ccadic/SHARPIW0/20211212_194929.jpg

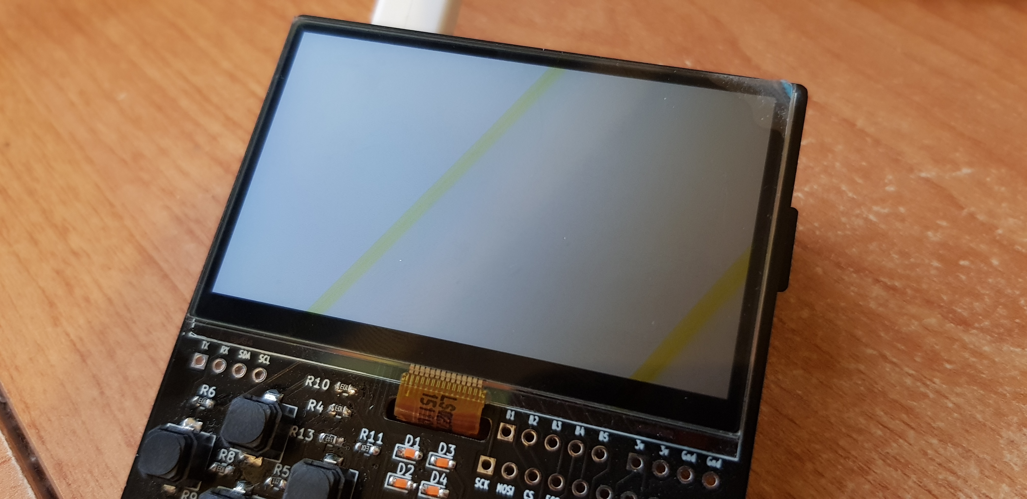
20211212_194929.jpg
