ccadic/SHARPIW0/20211215_131525.jpg

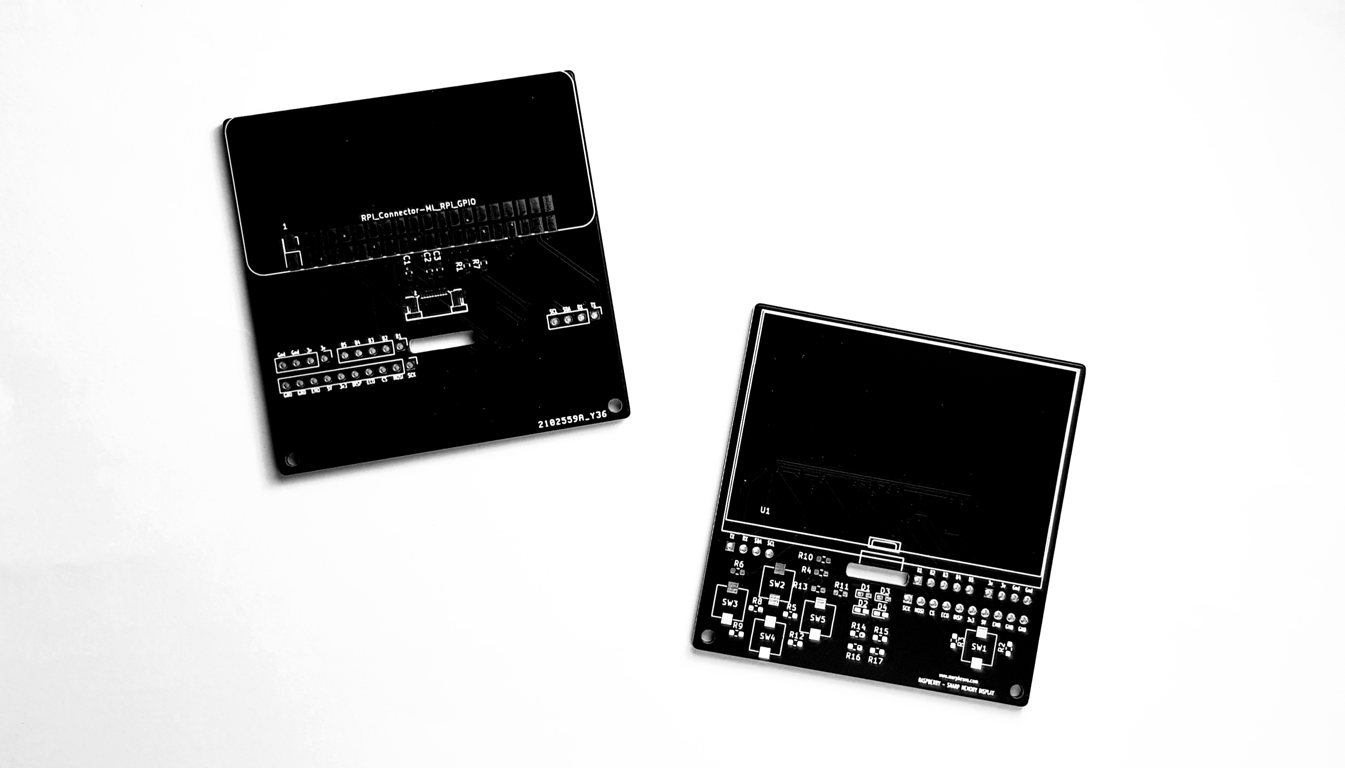
20211215_131525.jpg
